NestorIT/PH-1200/Docs/Images/PH-1200-360-1.png

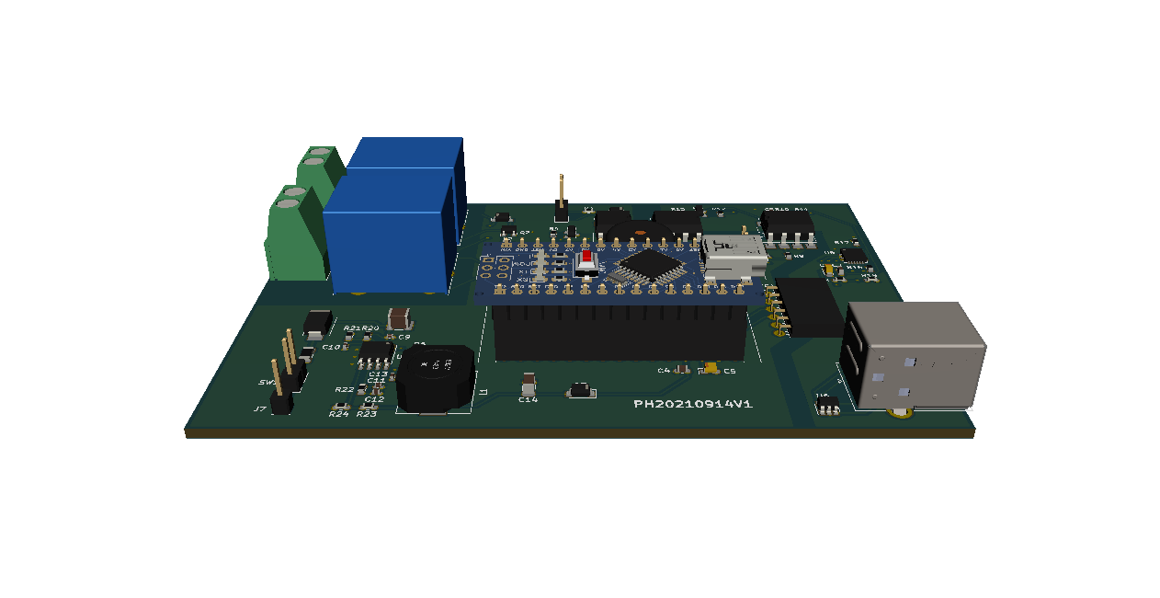
Docs/Images/PH-1200-360-1.png
