NestorIT/PH-1200/Docs/Images/PH-1200-botton.png

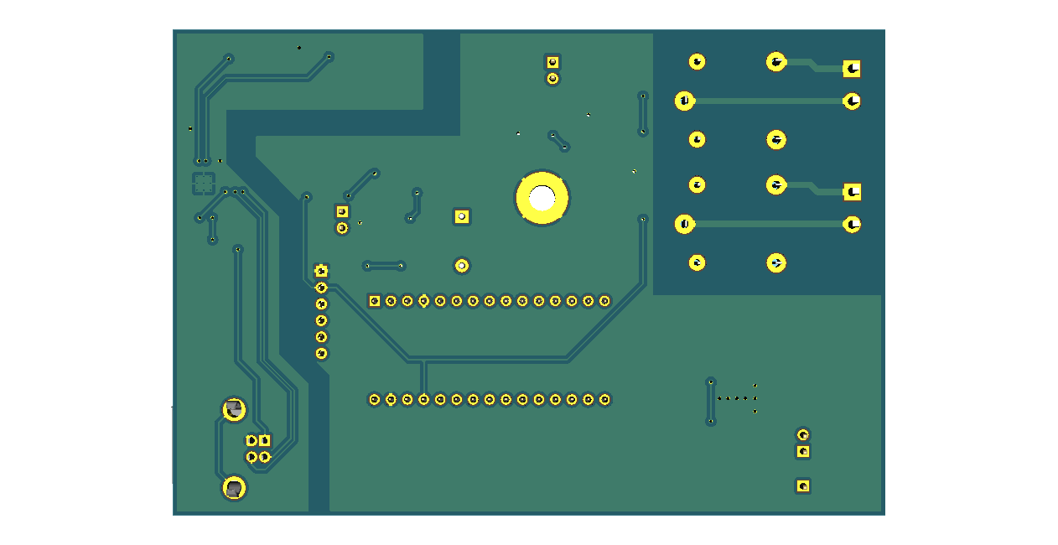
Docs/Images/PH-1200-botton.png
